gowenrw/3d6_badge/art/3d6art1.jpg

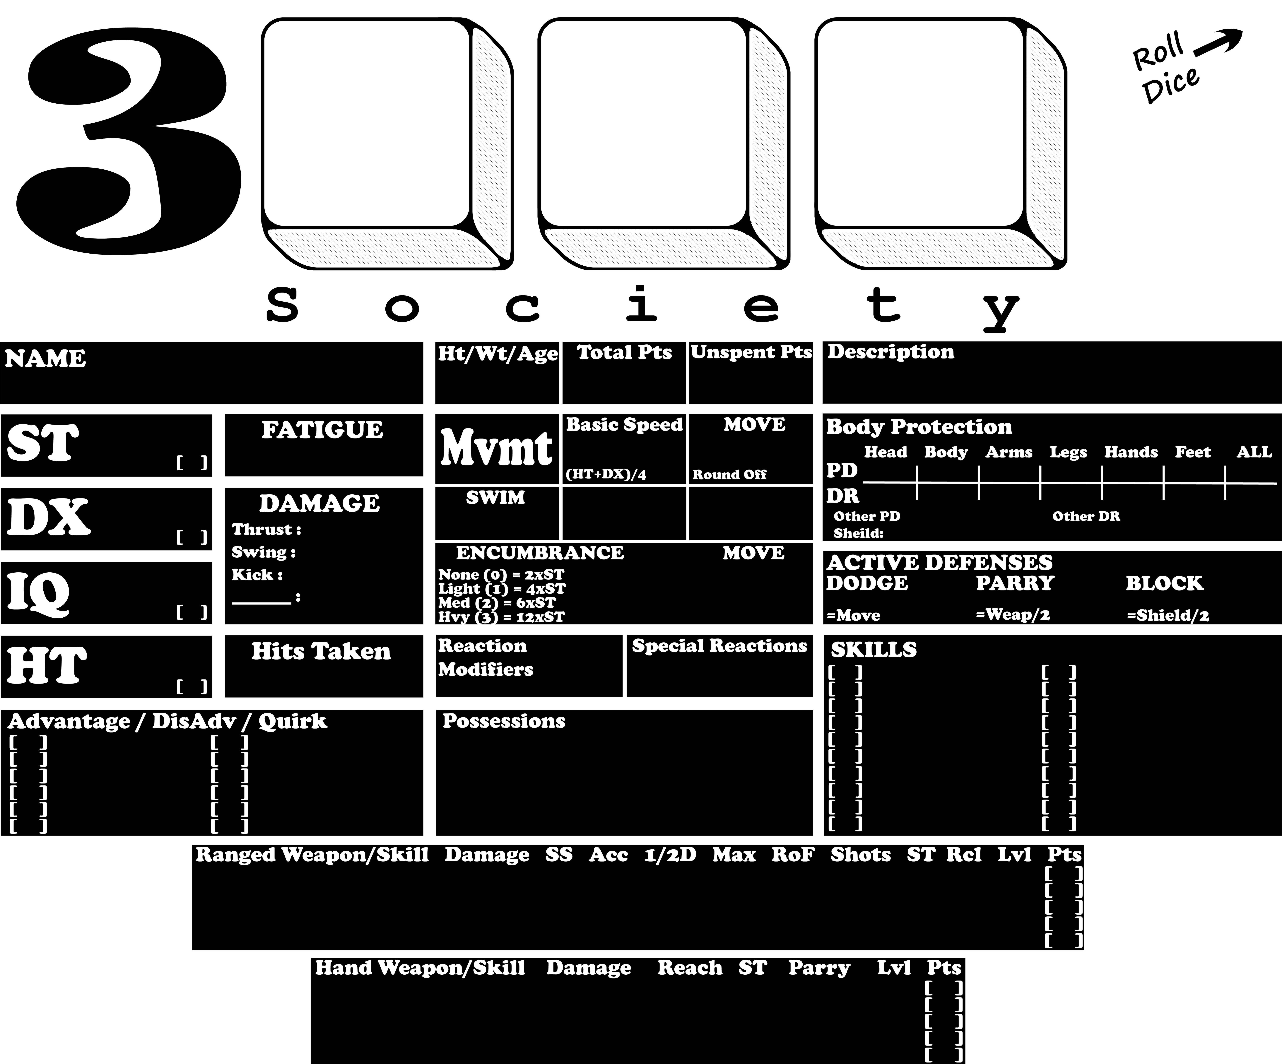
art/3d6art1.jpg
