gowenrw/3d6_badge/art/3d6textback1.jpg

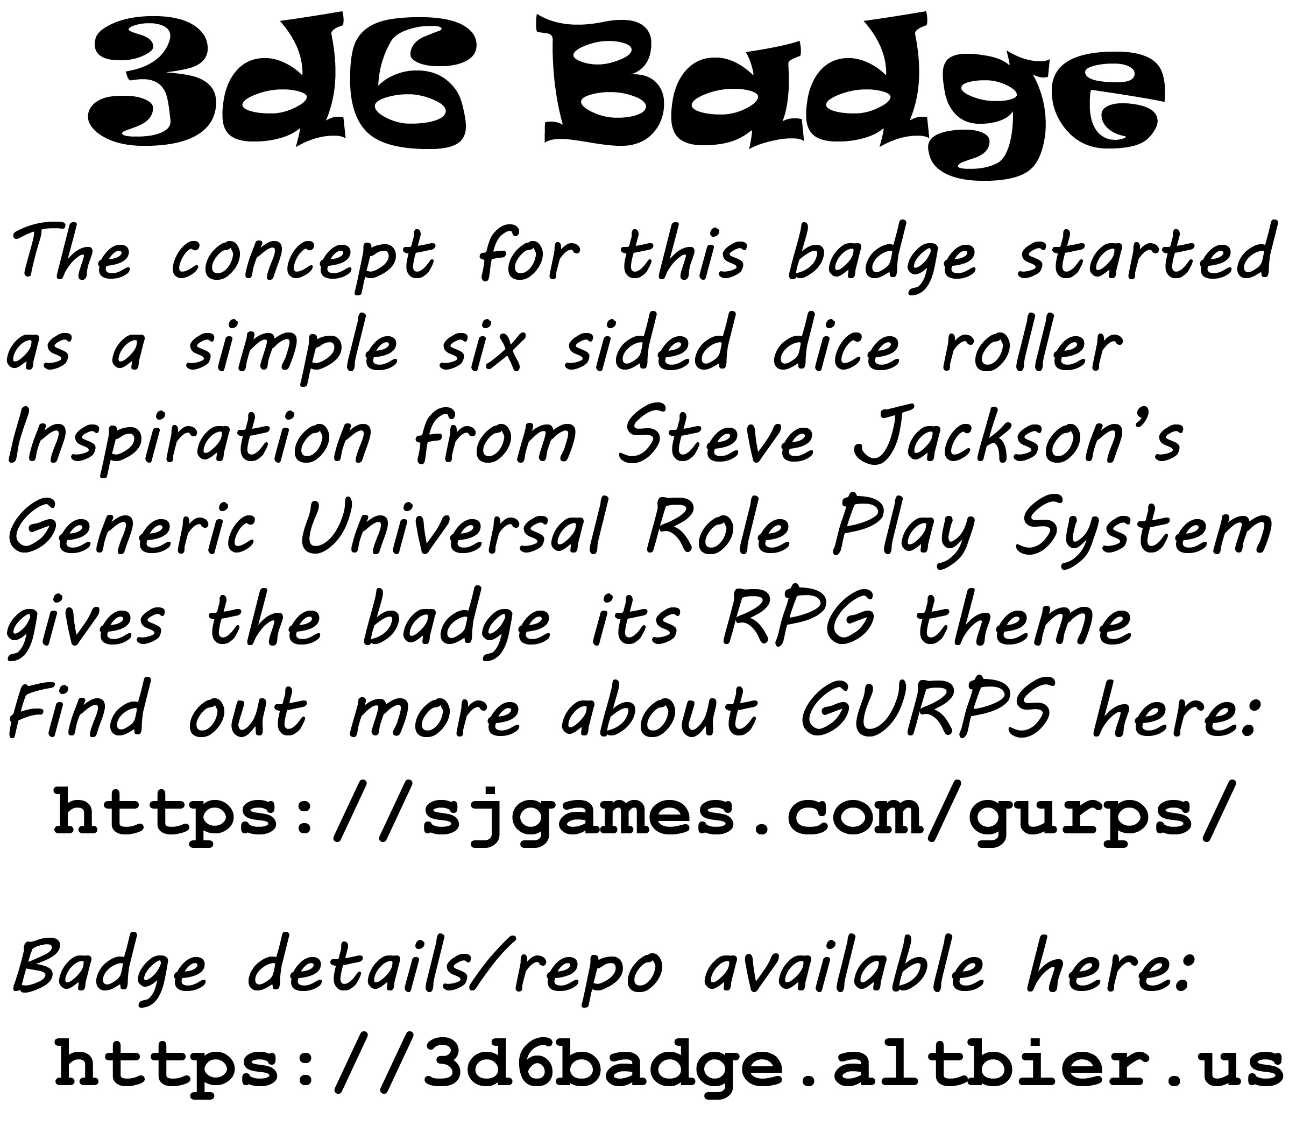
art/3d6textback1.jpg
