gowenrw/3d6_badge/art/3000-black-white-full-1080.png

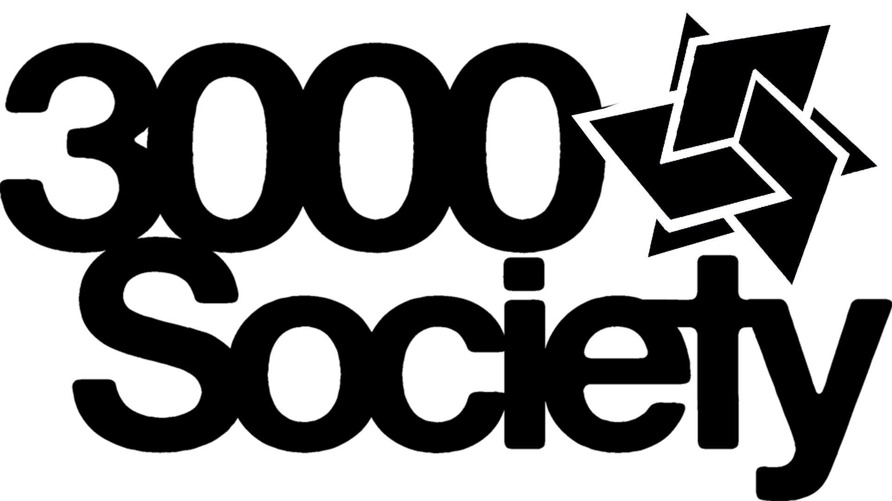
art/3000-black-white-full-1080.png
