gowenrw/3d6_badge/art/Margaret-HandDrawn1.jpg

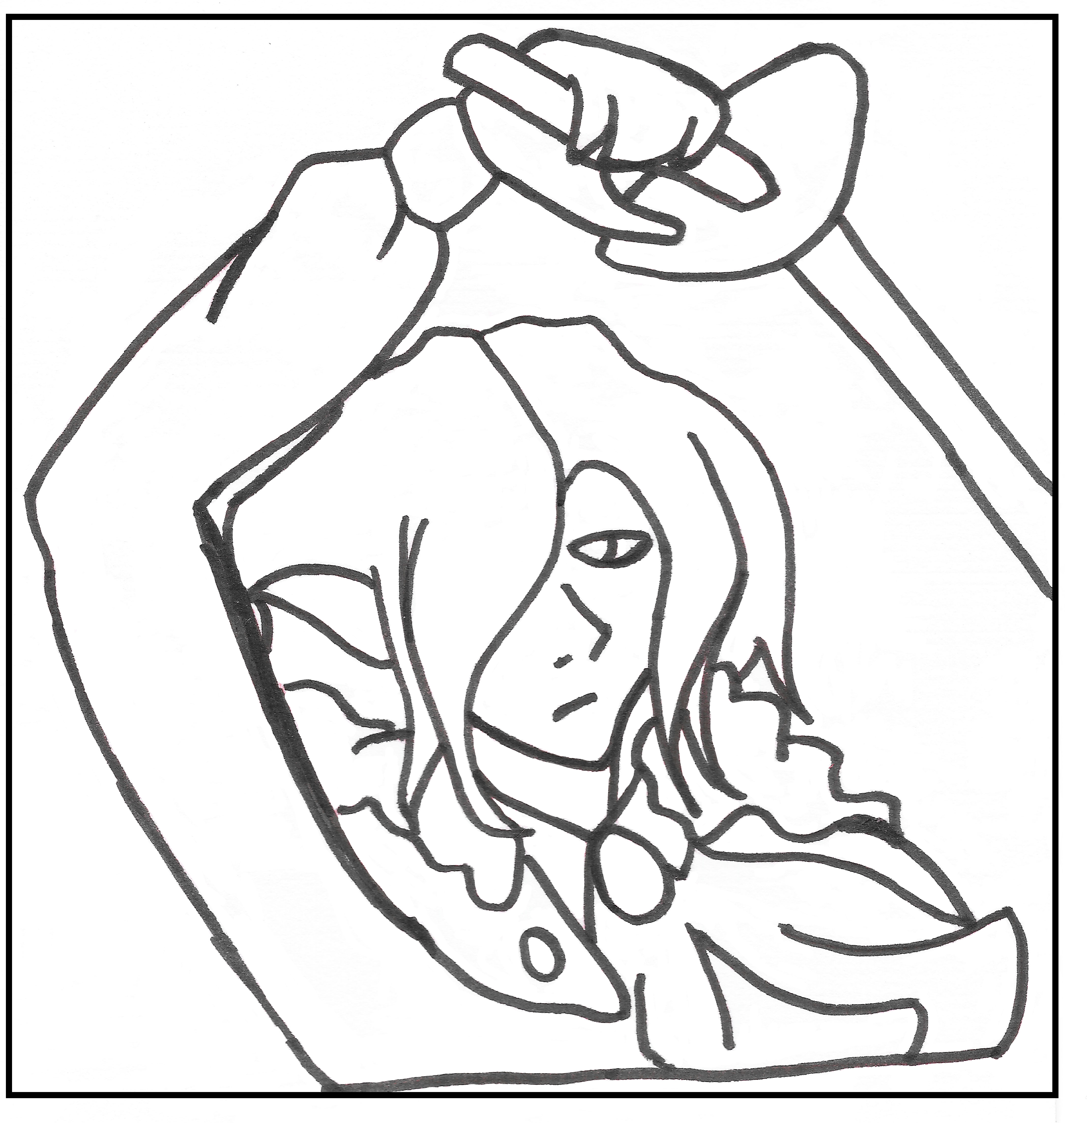
art/Margaret-HandDrawn1.jpg
