gowenrw/3d6_badge/art/Margaret-HandDrawn2.jpg

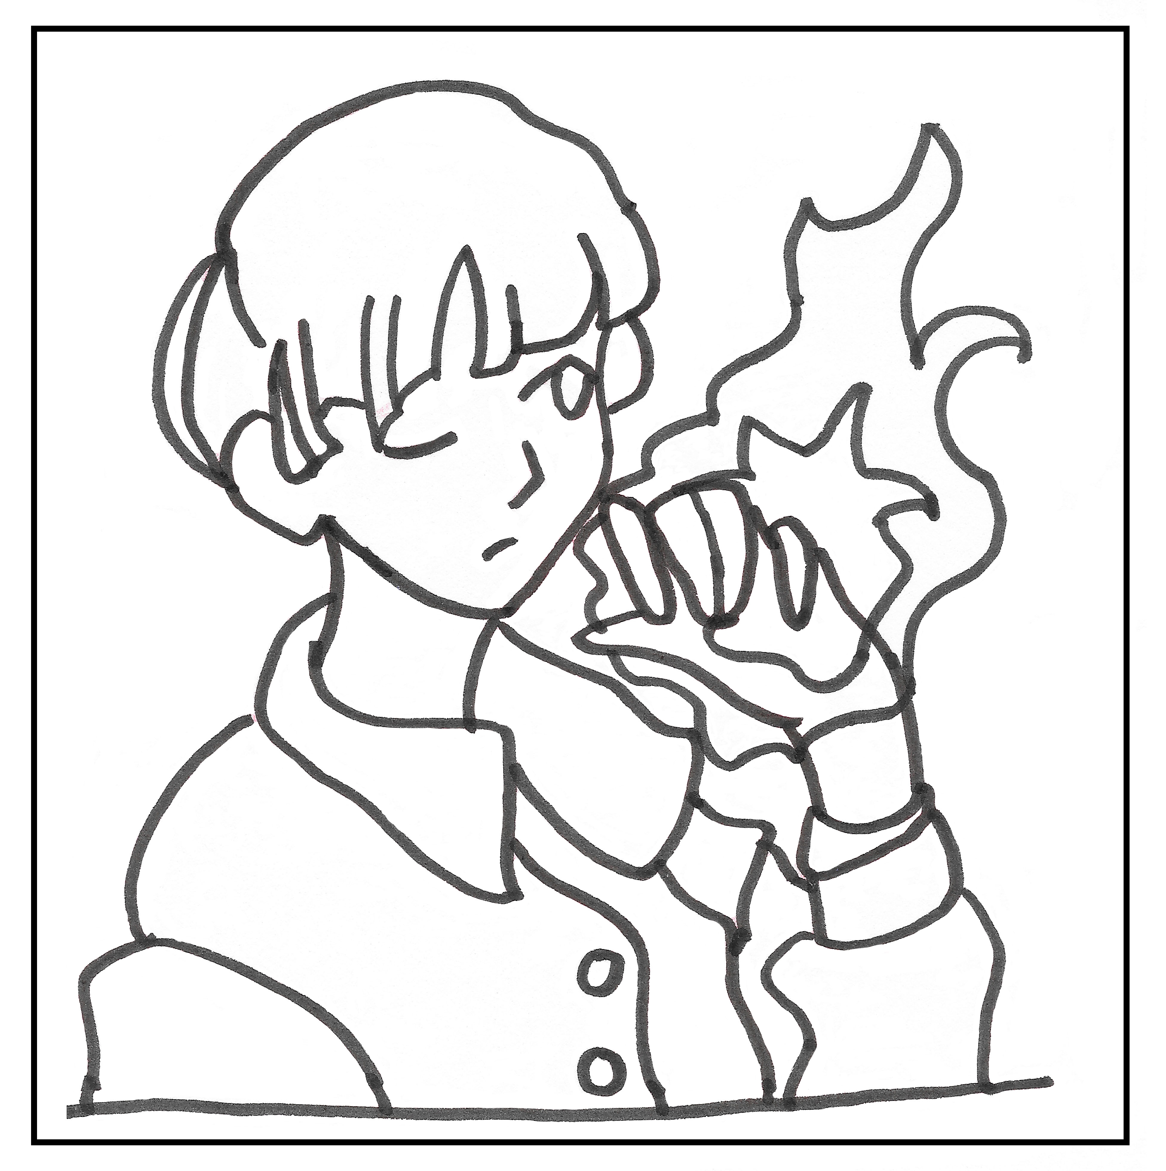
art/Margaret-HandDrawn2.jpg
