gowenrw/3d6_badge/eda/altbier_pcb_3d6/gerber/JLCPCB-DrillSettings.JPG

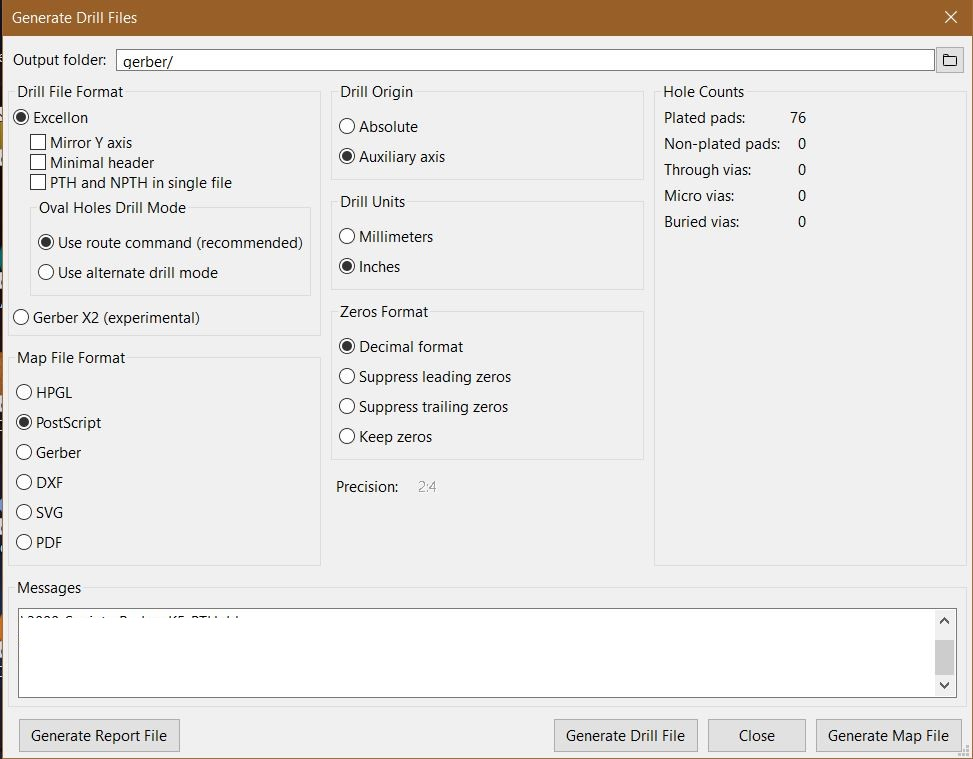
eda/altbier_pcb_3d6/gerber/JLCPCB-DrillSettings.JPG
