gowenrw/3d6_badge/eda/altbier_pcb_3d6/gerber/JLCPCB-GerberSetting.JPG

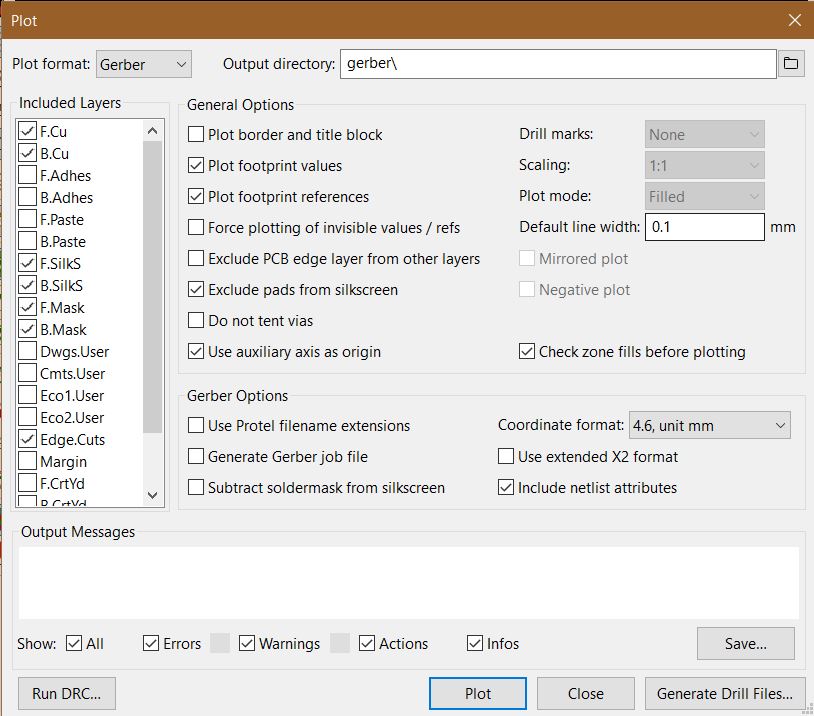
eda/altbier_pcb_3d6/gerber/JLCPCB-GerberSetting.JPG
