gowenrw/3d6_badge/eda/altbier_pcb_3d6/snapshots/altbier_pcb_3d6_3Dsnap4_small.jpg

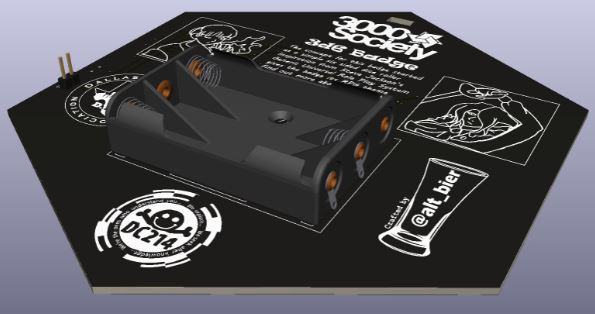
eda/altbier_pcb_3d6/snapshots/altbier_pcb_3d6_3Dsnap4_small.jpg
