gowenrw/3d6_badge/eda/altbier_pcb_3d6/3d_models/LED_D5.0mm-4_RGB.step

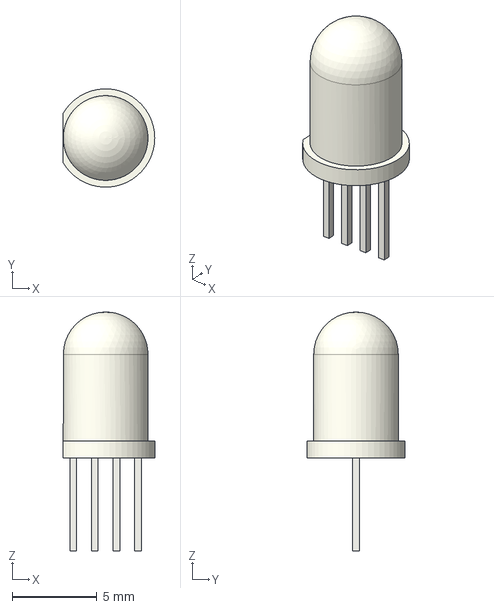
[picture p40: CAD file, 2021-02-14]
eda/altbier_pcb_3d6/3d_models/LED_D5.0mm-4_RGB.step
5.40 x 5.79 x 14.1 mm
