gowenrw/3d6_badge/eda/altbier_pcb_3d6/3d_models/R_0805_2012Metric.step

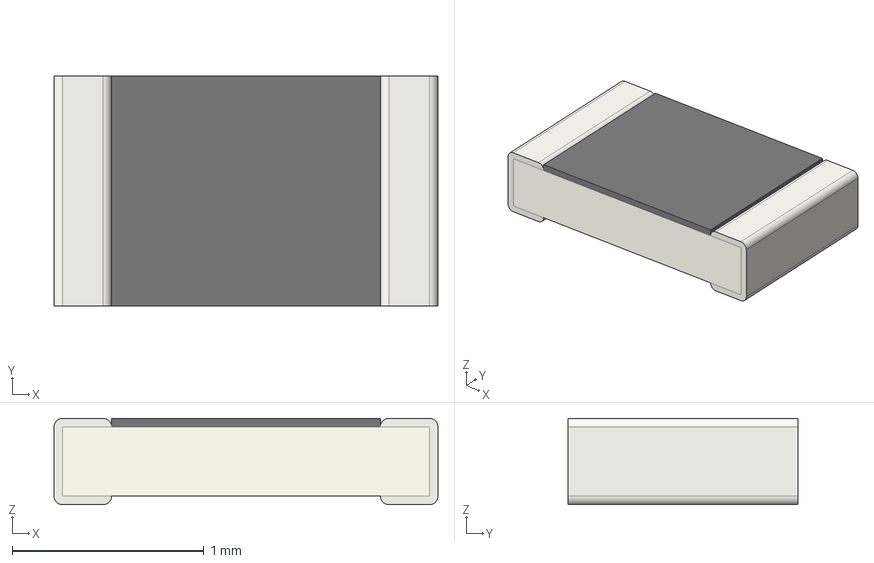
[picture p41: CAD file, 2021-02-14]
eda/altbier_pcb_3d6/3d_models/R_0805_2012Metric.step
2.00 x 1.20 x 0.45 mm
