gowenrw/3d6_badge/eda/altbier_pcb_3d6/3d_models/LED_0805_2012Metric_Castellated.step

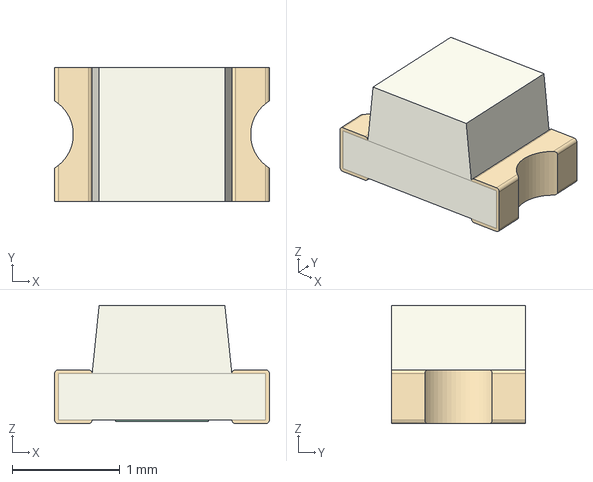
[picture p42: CAD file, 2021-02-14]
eda/altbier_pcb_3d6/3d_models/LED_0805_2012Metric_Castellated.step
2.00 x 1.25 x 1.10 mm
