gowenrw/3d6_badge/eda/altbier_pcb_3d6/3d_models/R_0603_1608Metric.step

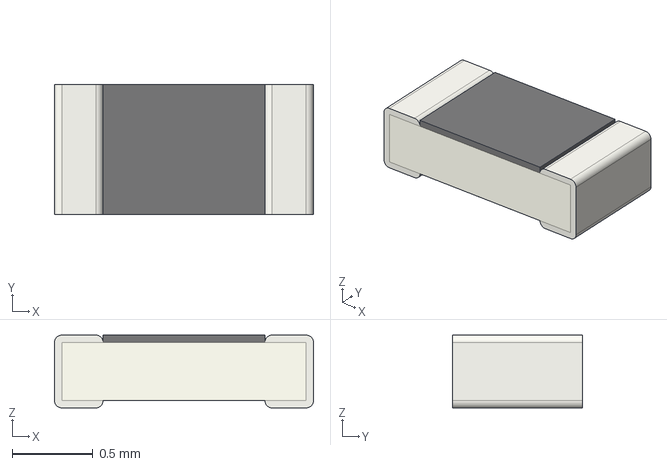
[picture p43: CAD file, 2021-02-14]
eda/altbier_pcb_3d6/3d_models/R_0603_1608Metric.step
1.60 x 0.8 x 0.45 mm
