gowenrw/3d6_badge/eda/altbier_pcb_3d6/3d_models/C_1206_3216Metric.step

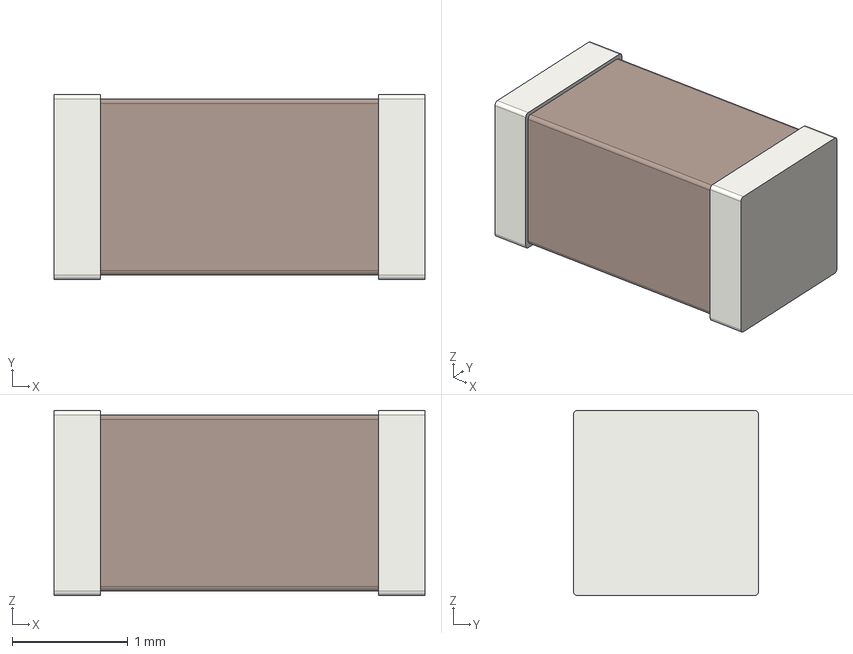
[picture p44: CAD file, 2021-02-14]
eda/altbier_pcb_3d6/3d_models/C_1206_3216Metric.step
3.20 x 1.60 x 1.60 mm
