gowenrw/3d6_badge/eda/altbier_pcb_3d6/3d_models/PinHeader_1x02_P2.54mm_Vertical.step

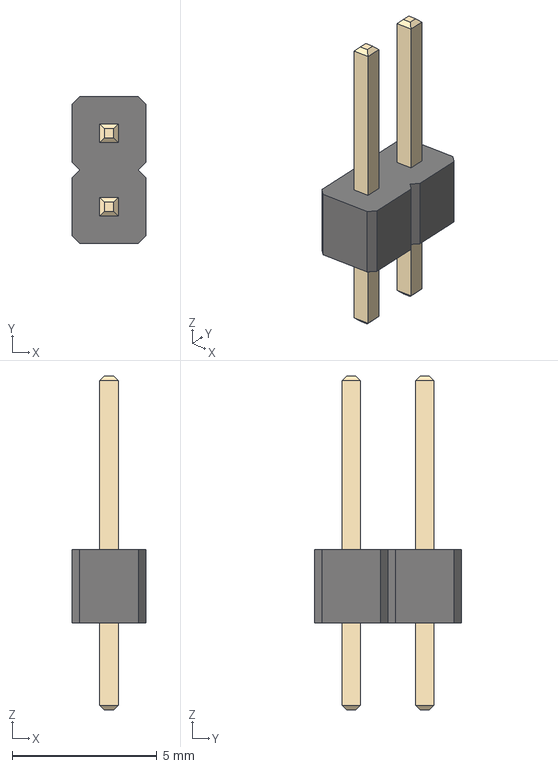
[picture p45: CAD file, 2021-02-14]
eda/altbier_pcb_3d6/3d_models/PinHeader_1x02_P2.54mm_Vertical.step
2.54 x 5.08 x 11.5 mm
