gowenrw/3d6_badge/eda/altbier_pcb_3d6/3d_models/C_Disc_D3.0mm_W2.0mm_P2.50mm.step

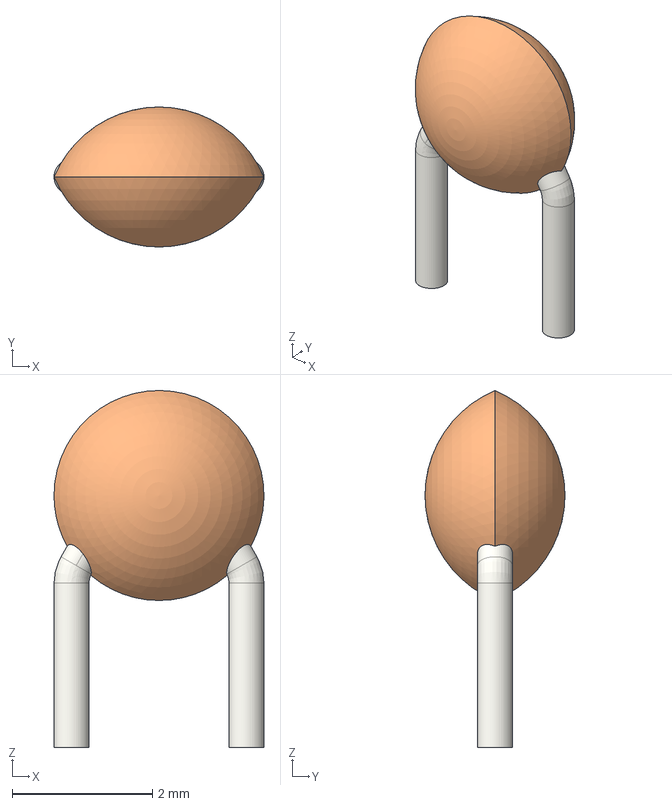
[picture p46: CAD file, 2021-02-14]
eda/altbier_pcb_3d6/3d_models/C_Disc_D3.0mm_W2.0mm_P2.50mm.step
3.00 x 2.00 x 5.10 mm
