gowenrw/3d6_badge/eda/altbier_pcb_3d6/3d_models/R_Axial_DIN0204_L3.6mm_D1.6mm_P5.08mm_Horizontal.step

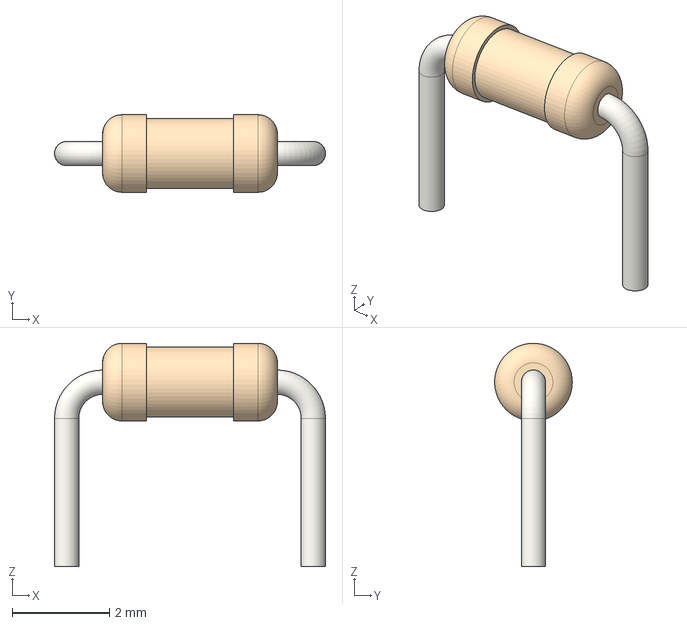
[picture p47: CAD file, 2021-02-14]
eda/altbier_pcb_3d6/3d_models/R_Axial_DIN0204_L3.6mm_D1.6mm_P5.08mm_Horizontal.step
5.58 x 1.60 x 4.60 mm
