gowenrw/3d6_badge/eda/altbier_pcb_3d6/3d_models/TS2306A.step

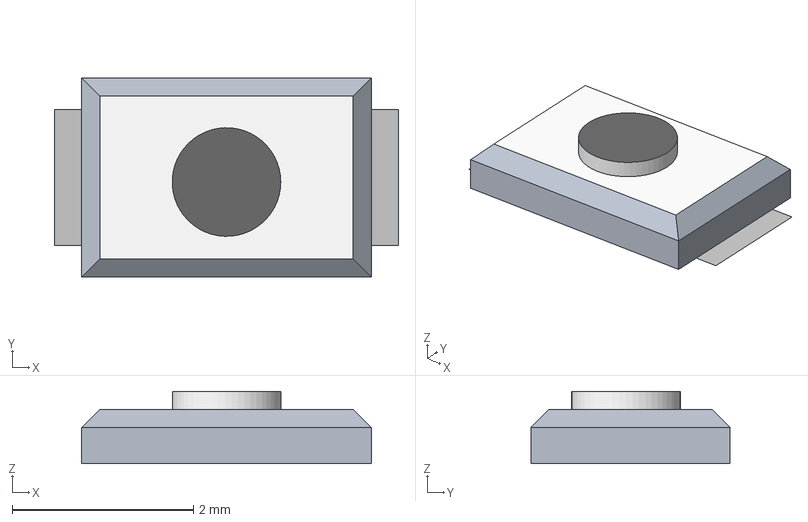
[picture p48: CAD file, 2021-02-14]
eda/altbier_pcb_3d6/3d_models/TS2306A.step
3.80 x 2.20 x 0.8 mm
Plane
