gowenrw/3d6_badge/eda/altbier_pcb_3d6/3d_models/SW_SPDT_PCM12.step

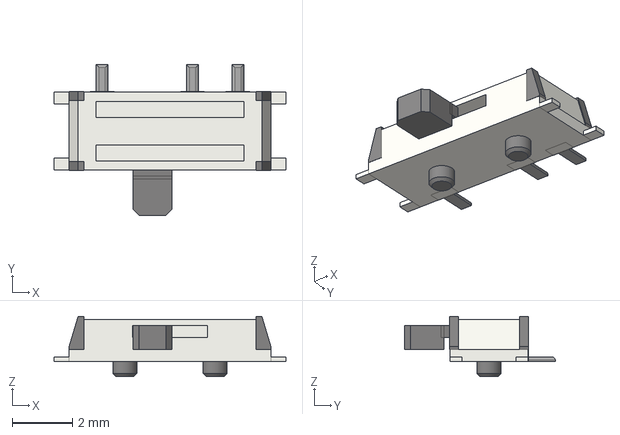
[picture p49: CAD file, 2021-02-14]
eda/altbier_pcb_3d6/3d_models/SW_SPDT_PCM12.step
7.70 x 5.00 x 2.00 mm
