gowenrw/3d6_badge/eda/altbier_pcb_3d6/3d_models/C_Rect_L4.6mm_W2.0mm_P2.50mm_MKS02_FKP02.step

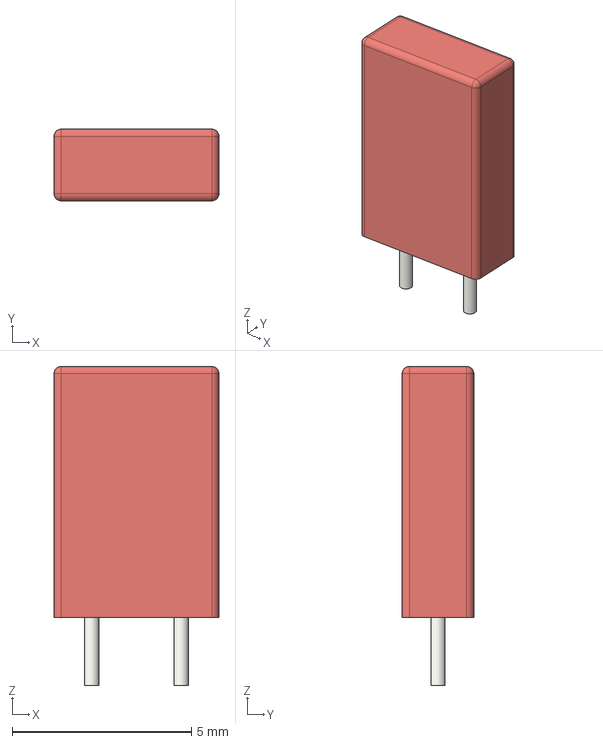
[picture p50: CAD file, 2021-02-14]
eda/altbier_pcb_3d6/3d_models/C_Rect_L4.6mm_W2.0mm_P2.50mm_MKS02_FKP02.step
4.60 x 2.00 x 8.90 mm
