gowenrw/3d6_badge/eda/altbier_pcb_3d6/3d_models/PinHeader_1x08_P2.54mm_Horizontal.step

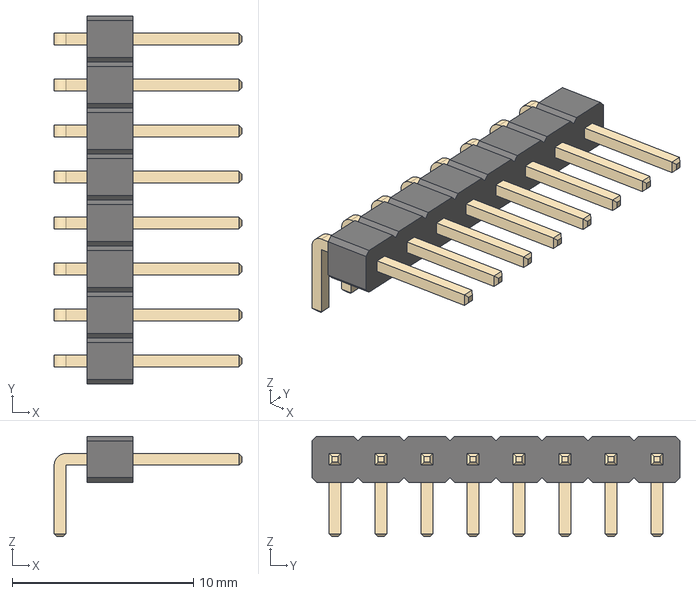
[picture p51: CAD file, 2021-02-14]
eda/altbier_pcb_3d6/3d_models/PinHeader_1x08_P2.54mm_Horizontal.step
10.4 x 20.3 x 5.54 mm
