gowenrw/3d6_badge/eda/altbier_pcb_3d6/3d_models/Battery_Holder_3xAAA_Simple.step

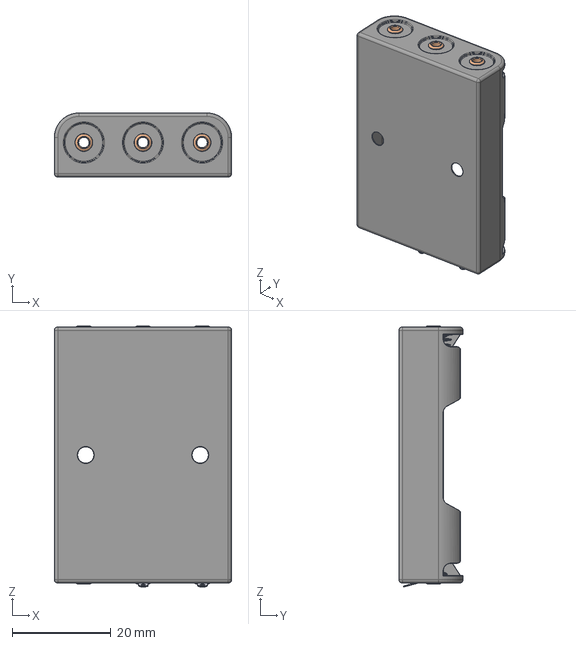
[picture p53: CAD file, 2021-02-14]
eda/altbier_pcb_3d6/3d_models/Battery_Holder_3xAAA_Simple.step
36.0 x 13.0 x 53.0 mm
