gowenrw/3d6_badge/eda/altbier_pcb_3d6/3d_models/PinHeader_1x08_P2.54mm_Vertical.step

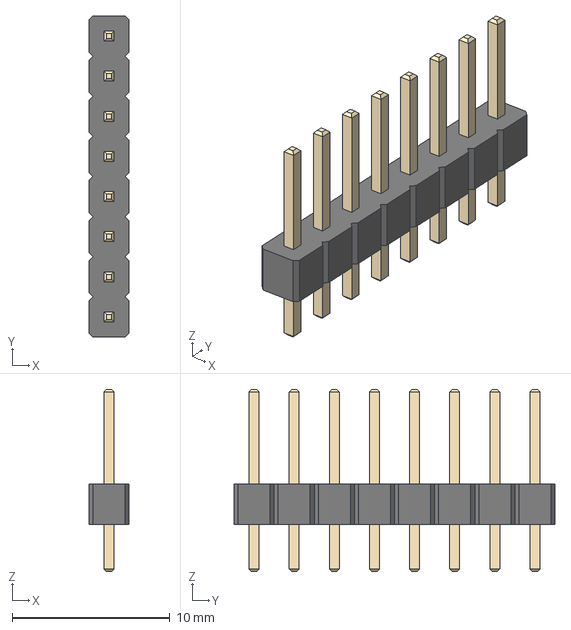
[picture p54: CAD file, 2021-02-14]
eda/altbier_pcb_3d6/3d_models/PinHeader_1x08_P2.54mm_Vertical.step
2.54 x 20.3 x 11.5 mm
