gowenrw/3d6_badge/eda/altbier_pcb_3d6/3d_models/LED_D8.0mm.step

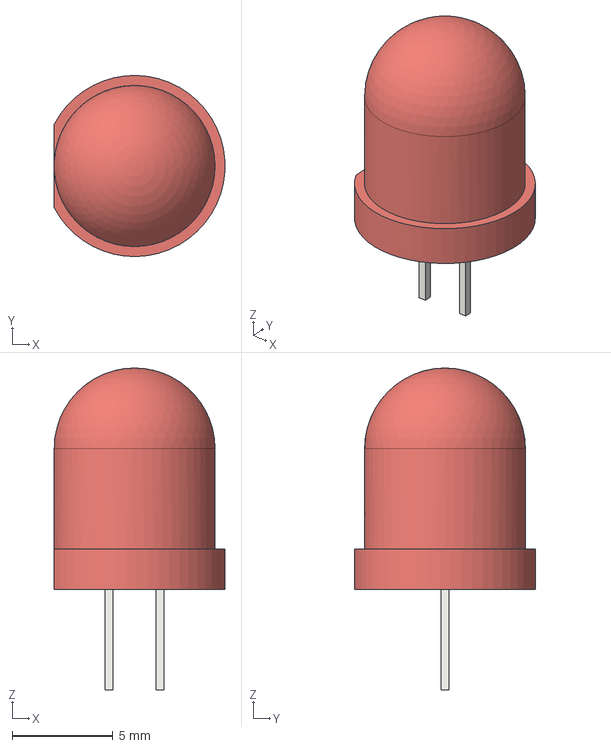
[picture p55: CAD file, 2021-02-14]
eda/altbier_pcb_3d6/3d_models/LED_D8.0mm.step
8.49 x 9.00 x 16.0 mm
